xddcore/Zero_Linux_Board/1.Hardware/1.1Zero_Linux_Board/JLCEDA/PCB_BOTTOM.jpeg

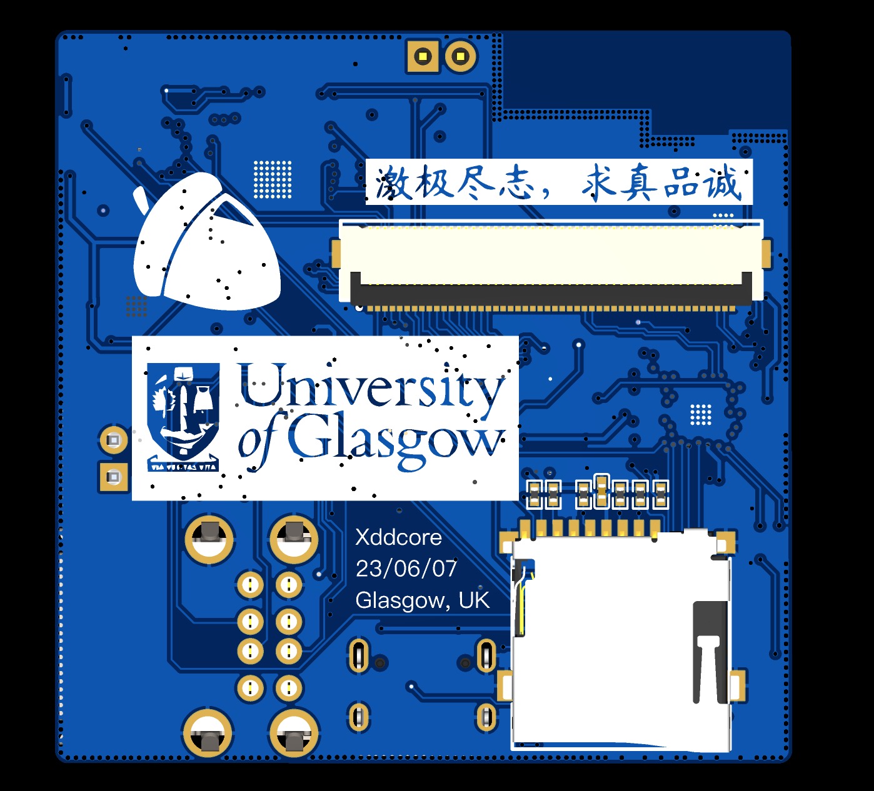
1.Hardware/1.1Zero_Linux_Board/JLCEDA/PCB_BOTTOM.jpeg
