xddcore/Zero_Linux_Board/1.Hardware/1.1Zero_Linux_Board/SHELL_BASIC/dwg_2.jpeg

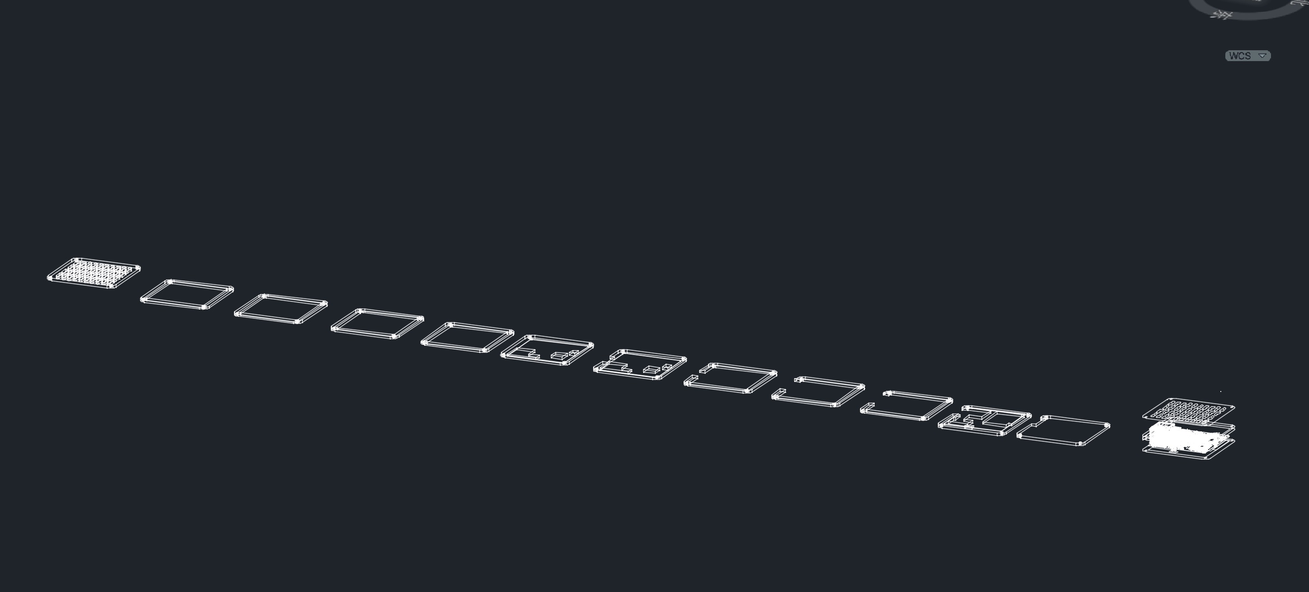
1.Hardware/1.1Zero_Linux_Board/SHELL_BASIC/dwg_2.jpeg
