xddcore/Zero_Linux_Board/1.Hardware/1.3MINI_PC_Board/JLCEDA/3D_PCB1_2023-08-30.png

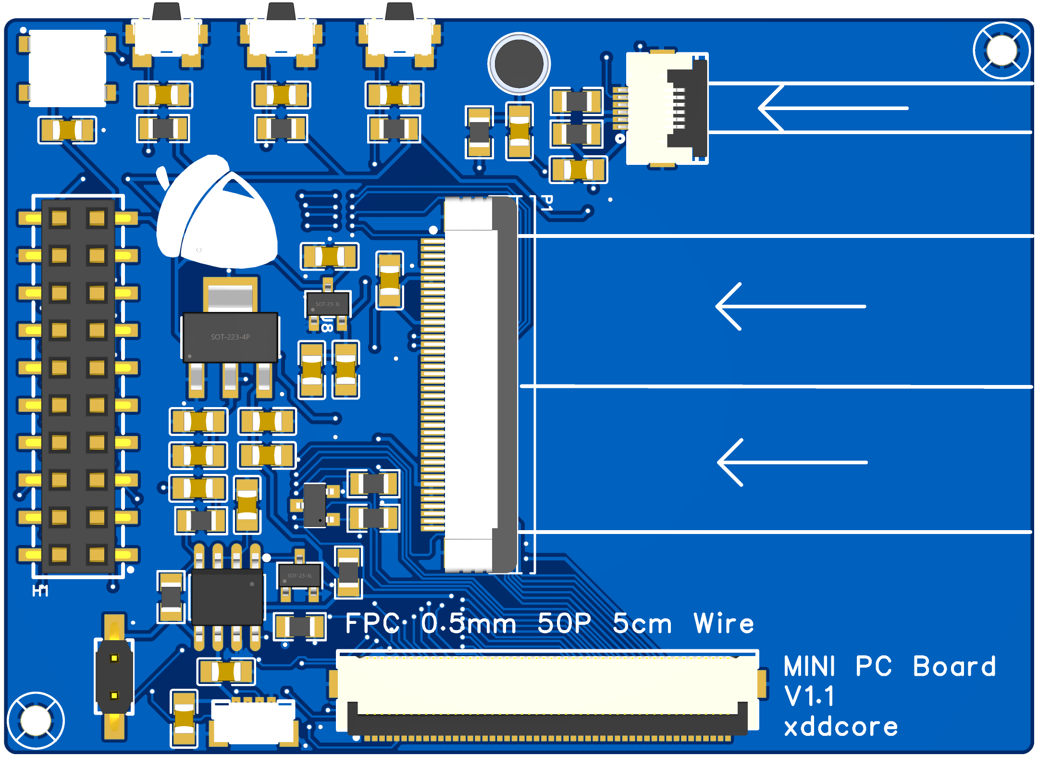
1.Hardware/1.3MINI_PC_Board/JLCEDA/3D_PCB1_2023-08-30.png
