xddcore/Zero_Linux_Board/1.Hardware/1.3MINI_PC_Board/MINI_PC_SHELL/untitled.87.jpg

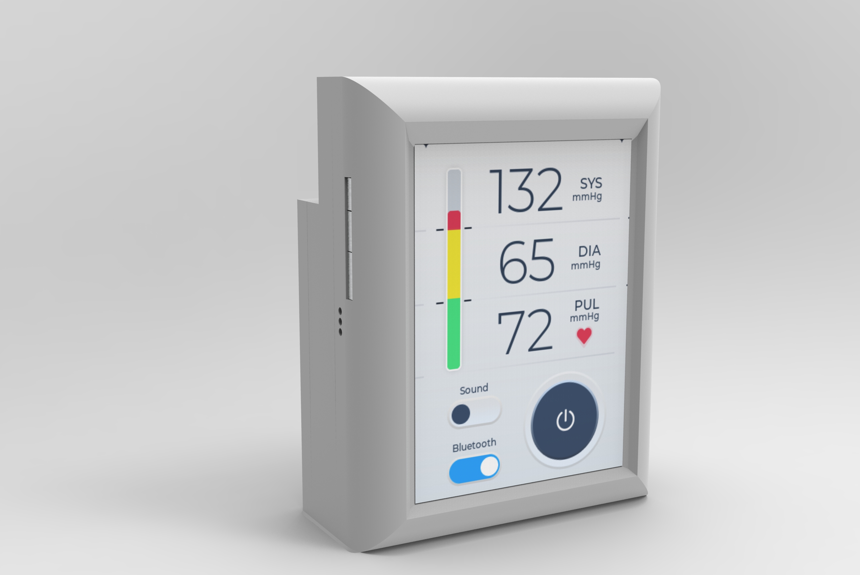
1.Hardware/1.3MINI_PC_Board/MINI_PC_SHELL/untitled.87.jpg
