xddcore/Zero_Linux_Board/image.png

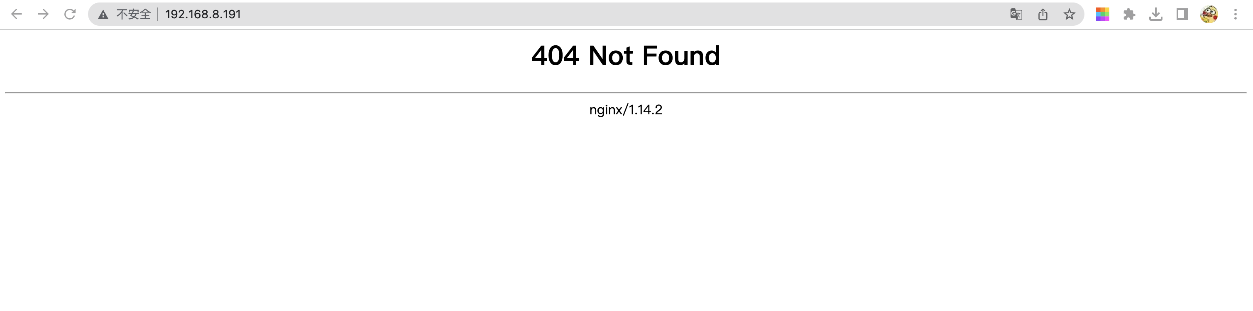
image.png
