xddcore/Zero_Linux_Board/img/Back_board_coin.jpg

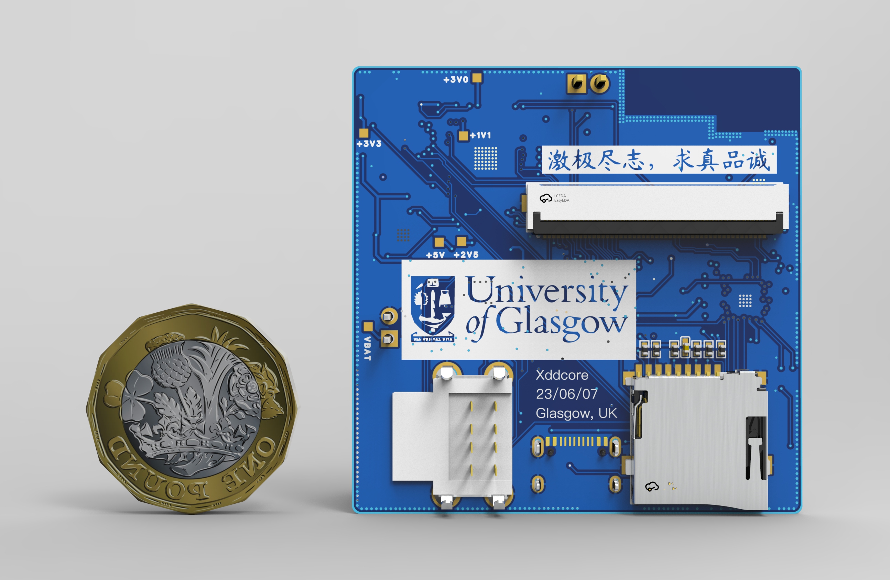
img/Back_board_coin.jpg
