xddcore/Zero_Linux_Board/img/Back_Board_Explore_Shell_2.jpg

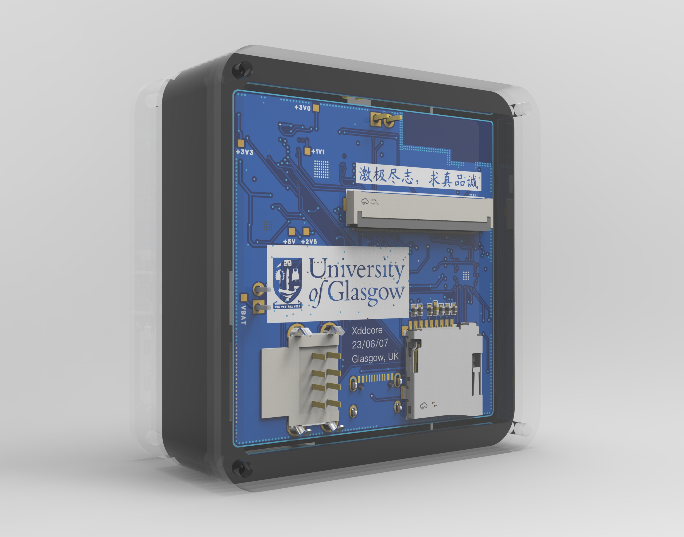
img/Back_Board_Explore_Shell_2.jpg
