xddcore/Zero_Linux_Board/img/Back_Board_Explore_Shell_3.jpg

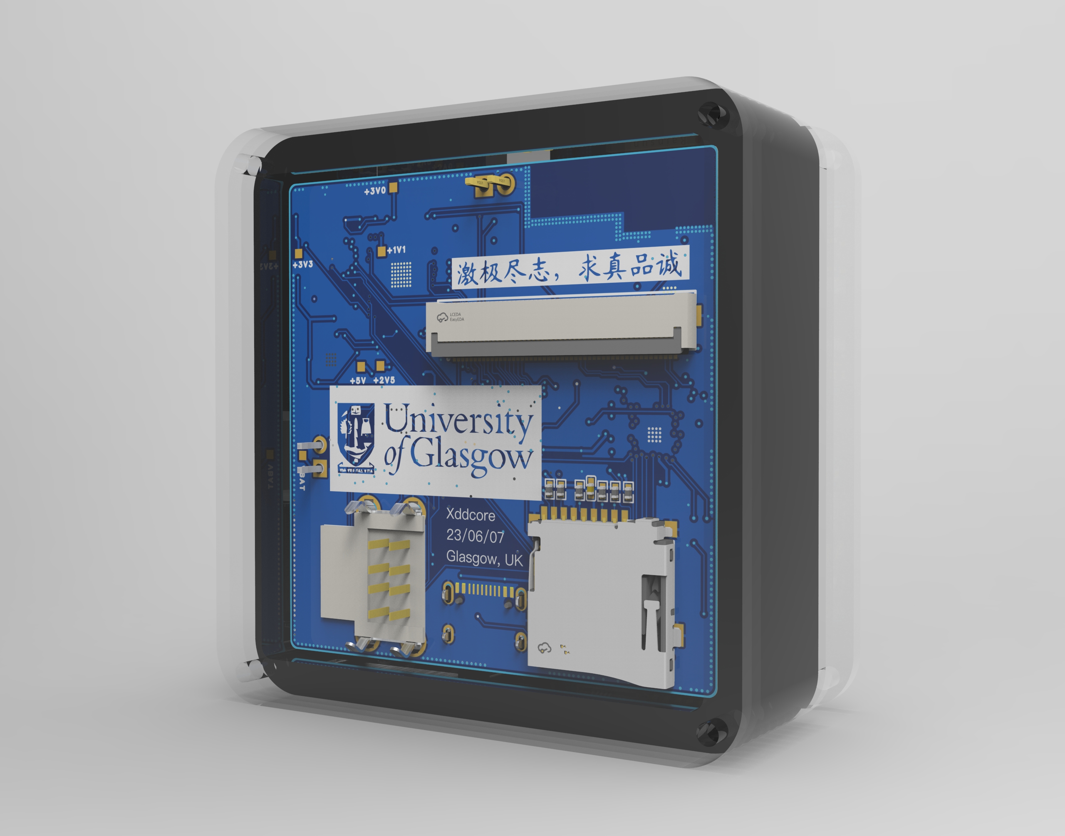
img/Back_Board_Explore_Shell_3.jpg
