xddcore/Zero_Linux_Board/img/Back_only_board.jpg

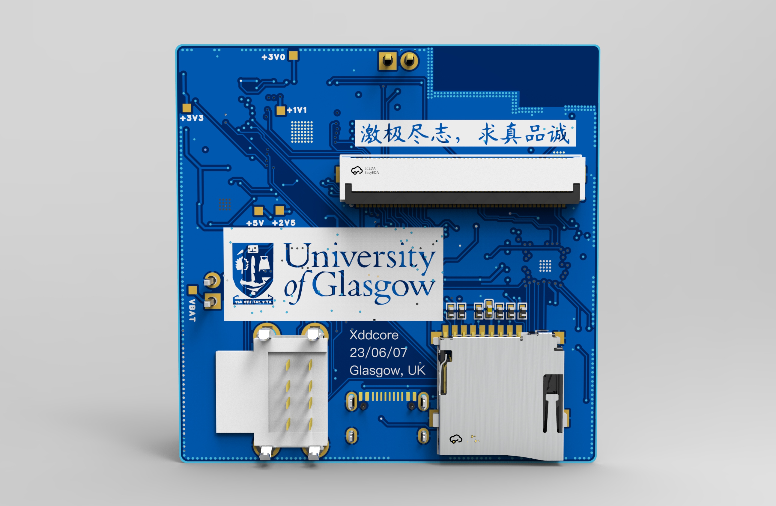
img/Back_only_board.jpg
