xddcore/Zero_Linux_Board/img/BiliBiliTV_Board1.jpg

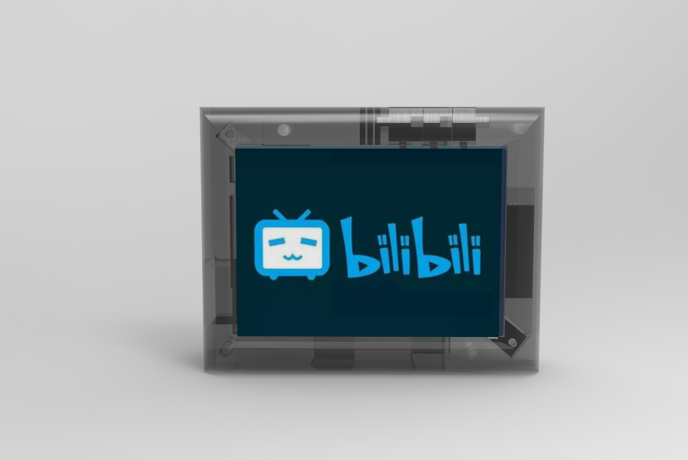
img/BiliBiliTV_Board1.jpg
