xddcore/Zero_Linux_Board/img/Front_Board_Basic_Shell_3.jpg

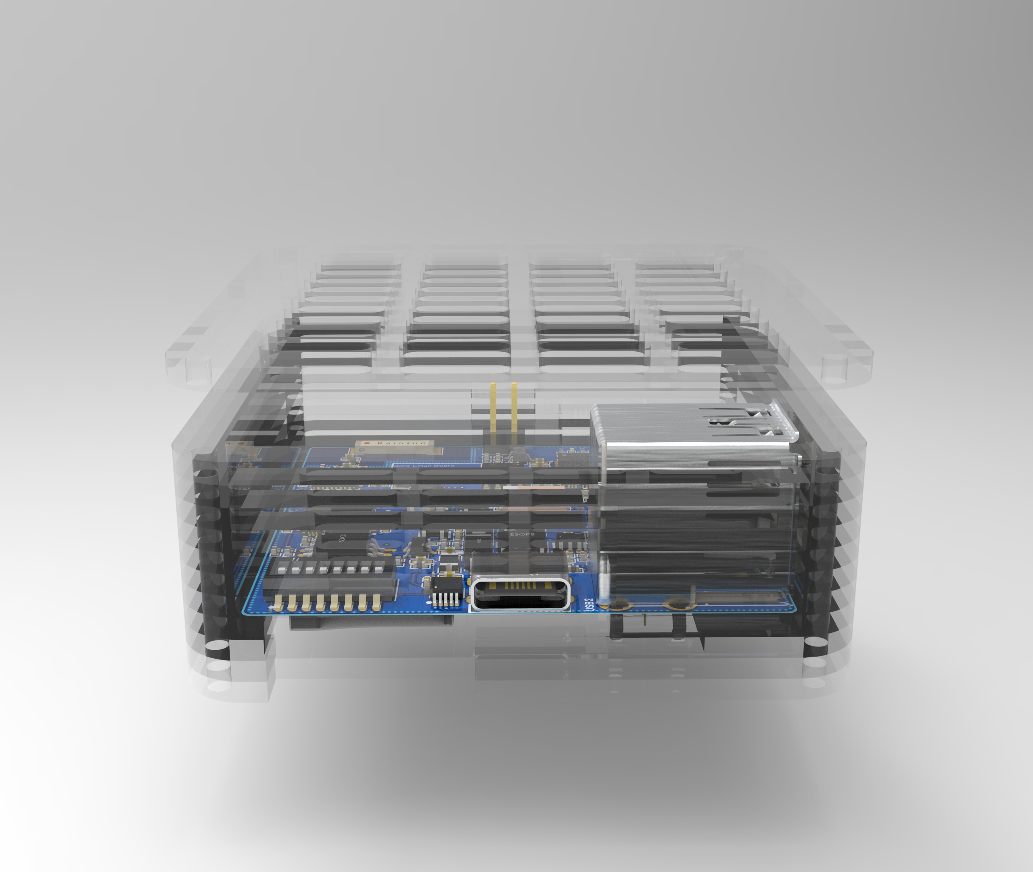
img/Front_Board_Basic_Shell_3.jpg
