xddcore/Zero_Linux_Board/img/Front_board_coin.jpg

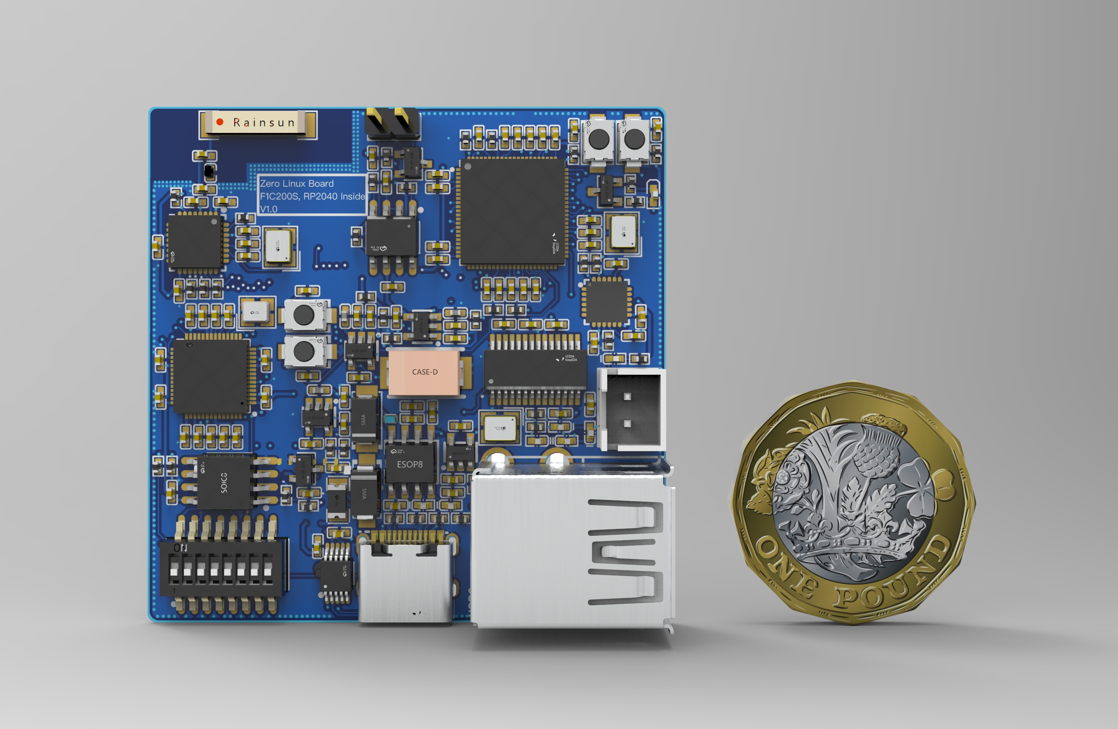
img/Front_board_coin.jpg
