xddcore/Zero_Linux_Board/img/Front_Board_Explore_Shell_3.jpg

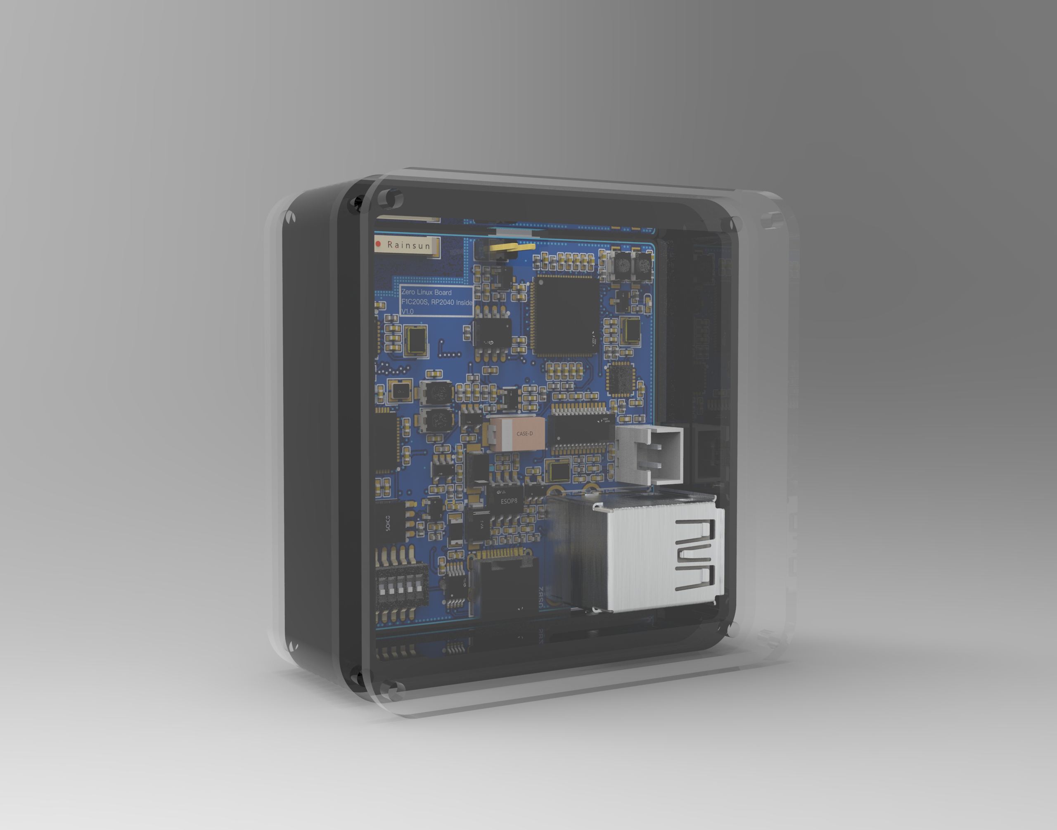
img/Front_Board_Explore_Shell_3.jpg
