xddcore/Zero_Linux_Board/img/Front_only_board.jpg

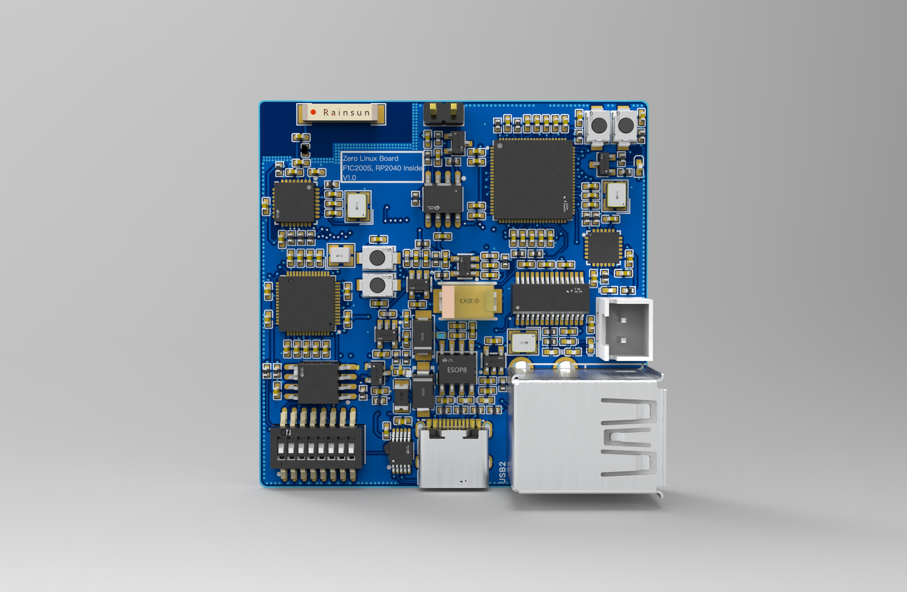
img/Front_only_board.jpg
