xddcore/Zero_Linux_Board/img/MINIPC_Board1.jpg

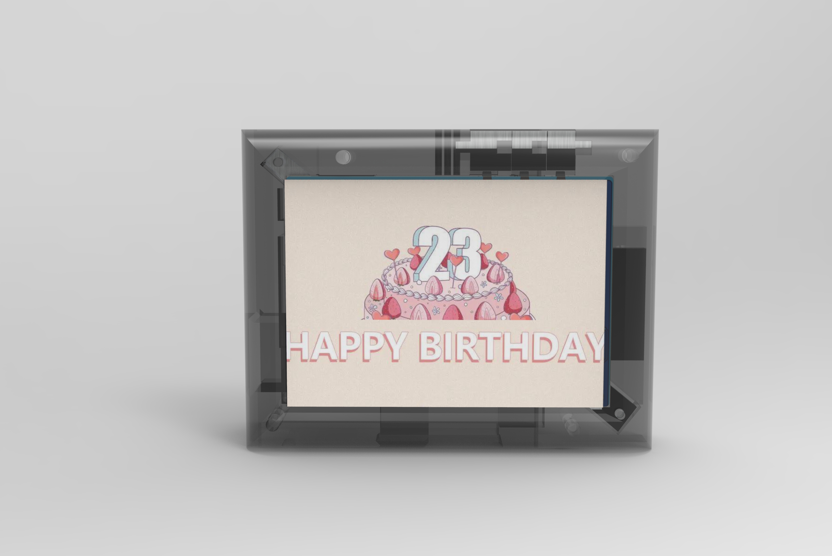
img/MINIPC_Board1.jpg
