xddcore/Zero_Linux_Board/img/MINIPC_Board2.jpg

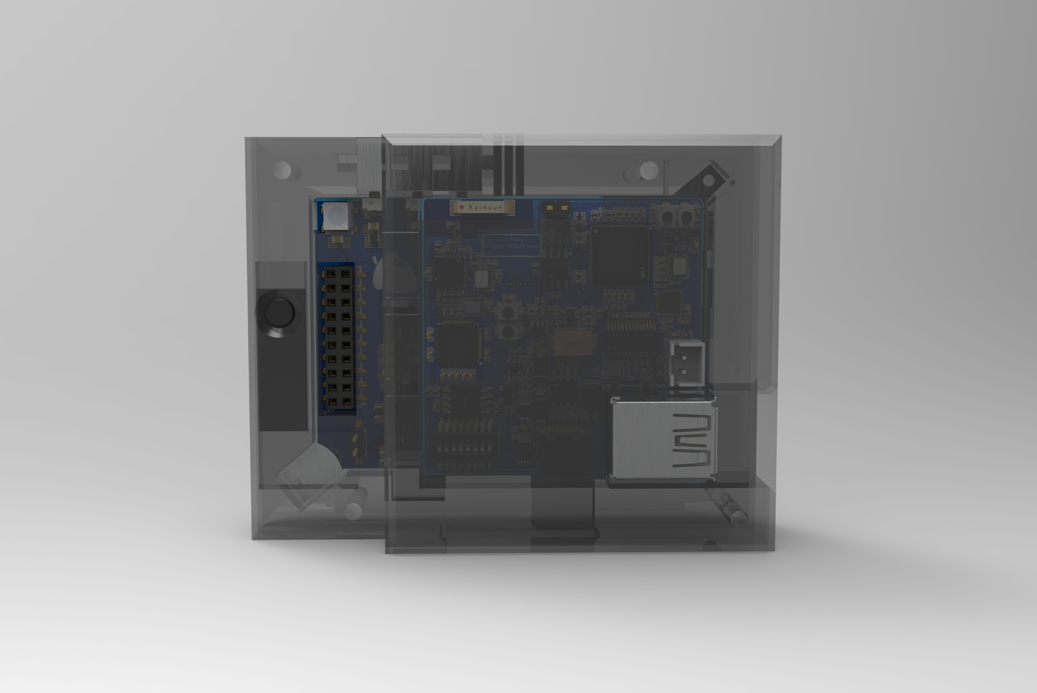
img/MINIPC_Board2.jpg
