xddcore/Zero_Linux_Board/img/PCB_Back.JPG

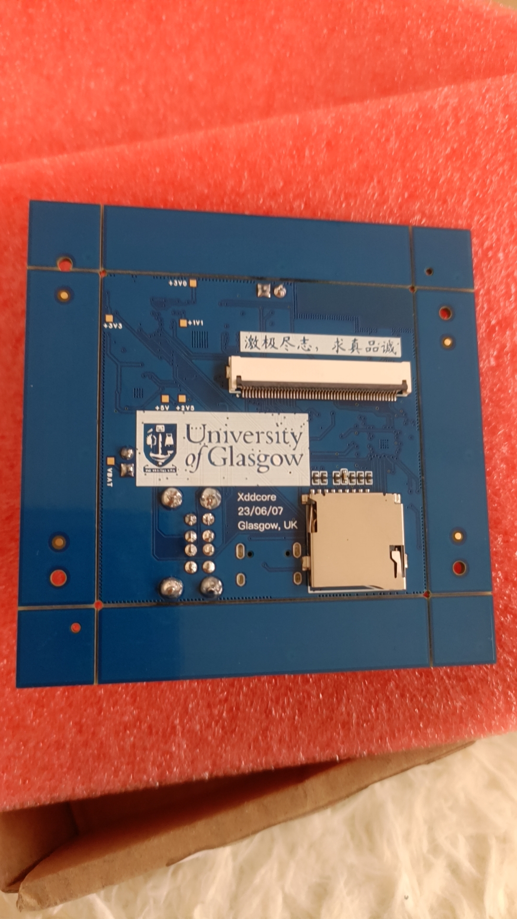
img/PCB_Back.JPG
