xddcore/Zero_Linux_Board/img/PCB_Front.JPG

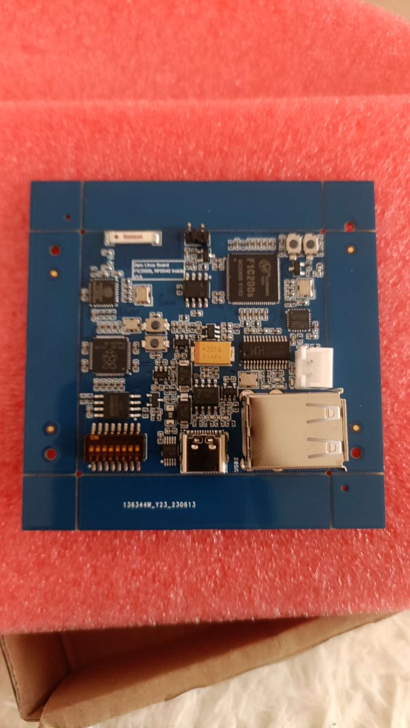
img/PCB_Front.JPG
