xddcore/Zero_Linux_Board/img/PCB_SMT.jpeg

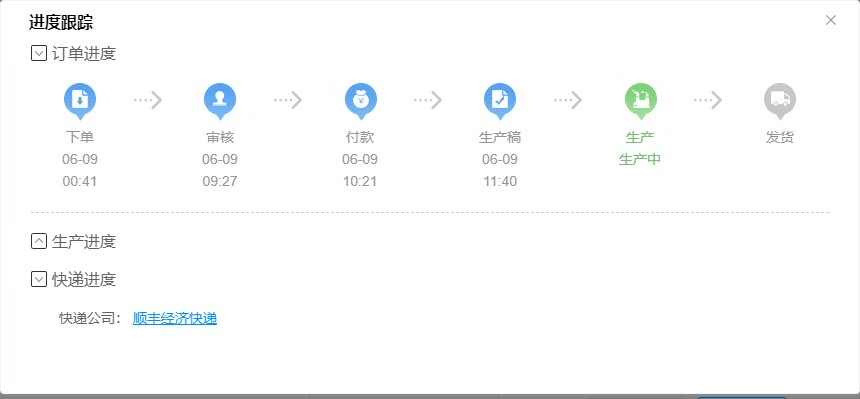
img/PCB_SMT.jpeg
