xddcore/Zero_Linux_Board/img/smt_group.jpeg

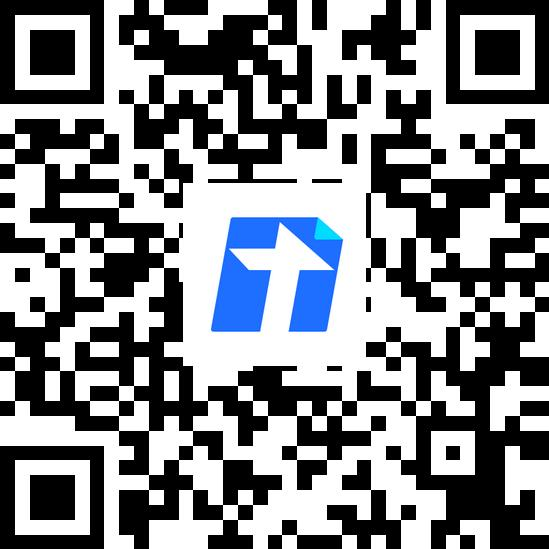
img/smt_group.jpeg
