xddcore/Zero_Linux_Board/img/Xmind.png

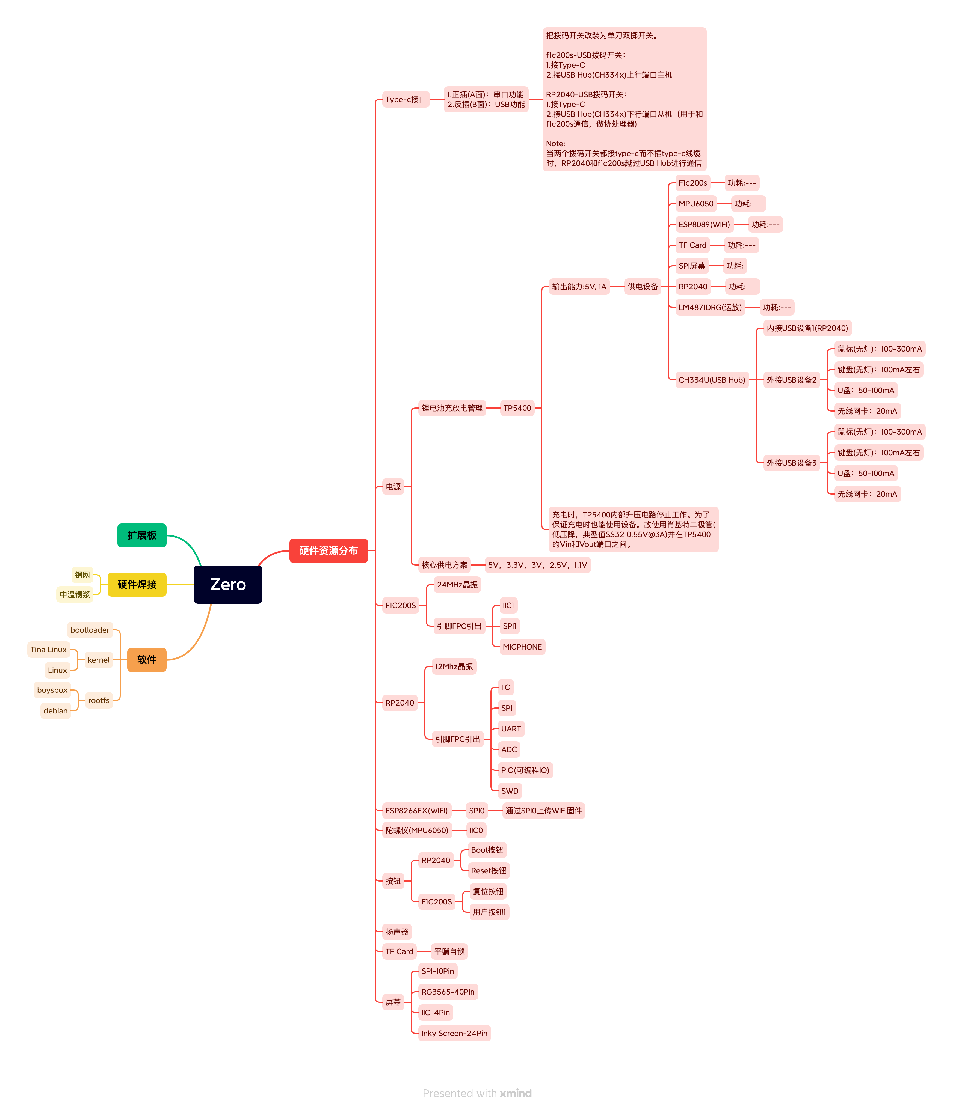
img/Xmind.png
